EvanLandau/modular-housing-system/Wall Cores/basic_wall.FCStd

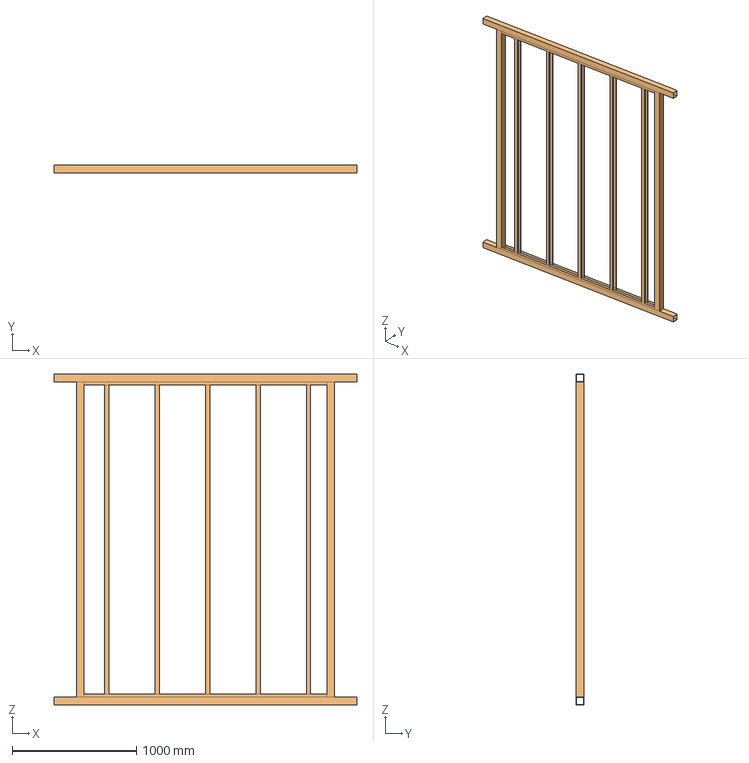
[picture p15: CAD file, 2021-06-02]
Wall Cores/basic_wall.FCStd
2438.4 x 63.5 x 2667.0 mm
Wall Inner Panel
Wall Inner Panel - Basic
