EvanLandau/modular-housing-system/Core Modules/medium_roof_slope_inside_corner.FCStd

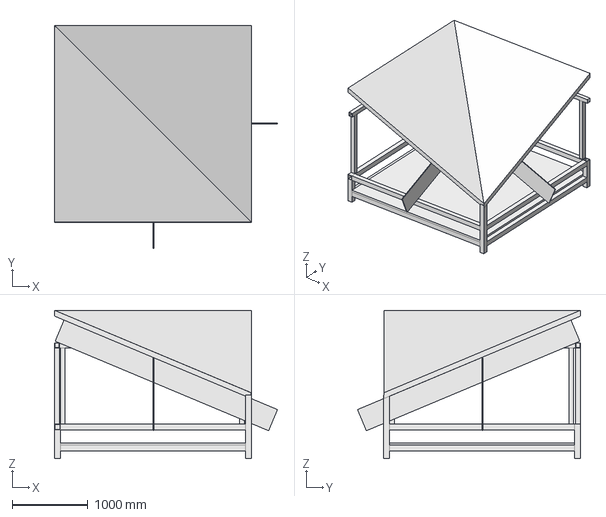
[picture p16: CAD file, 2021-06-02]
Core Modules/medium_roof_slope_inside_corner.FCStd
2936.2 x 2936.2 x 1953.9 mm
