EvanLandau/modular-housing-system/Core Modules/medium_roof_slope_outside_corner.FCStd

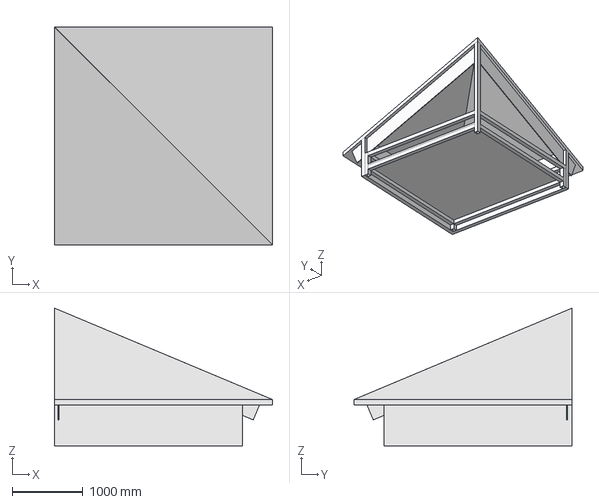
[picture p18: CAD file, 2021-06-02]
Core Modules/medium_roof_slope_outside_corner.FCStd
3092.4 x 3092.4 x 1953.8 mm
