EvanLandau/modular-housing-system/Other Modules/walk_in_closet.FCStd

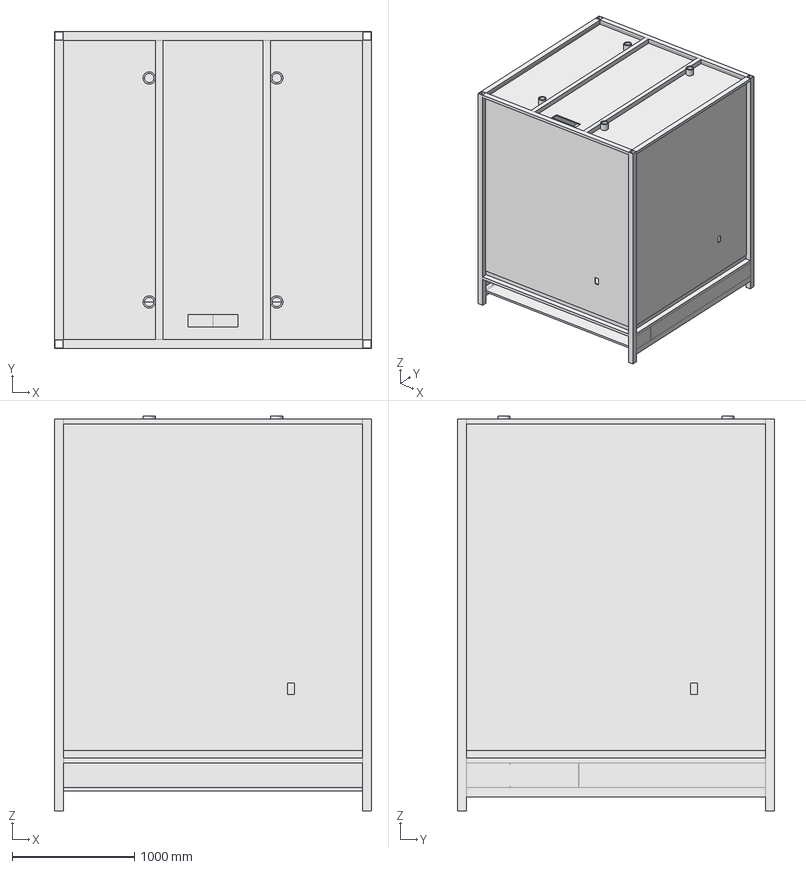
[picture p19: CAD file, 2021-06-02]
Other Modules/walk_in_closet.FCStd
2590.8 x 2590.8 x 3225.8 mm
