EvanLandau/modular-housing-system/Core Modules/bathroom_module.FCStd

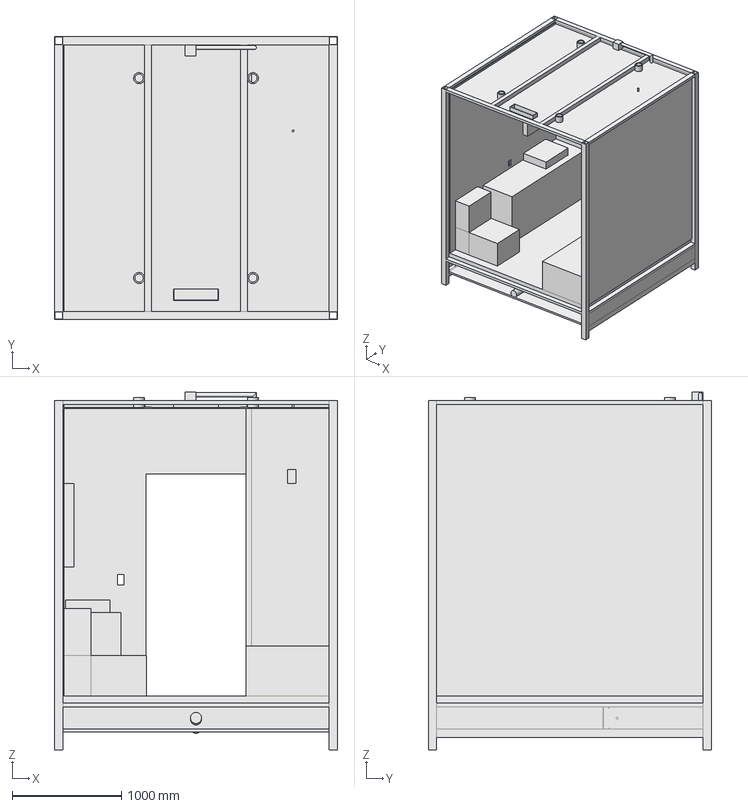
[picture p20: CAD file, 2021-06-02]
Core Modules/bathroom_module.FCStd
2590.8 x 2592.8 x 3276.6 mm
