EvanLandau/modular-housing-system/Other Modules/TV_room.FCStd

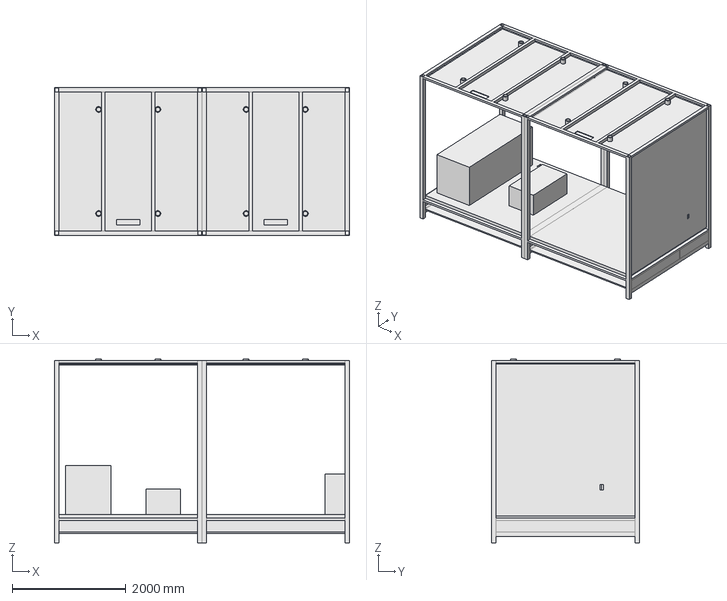
[picture p21: CAD file, 2021-06-02]
Other Modules/TV_room.FCStd
5181.6 x 2590.8 x 3225.8 mm
