EvanLandau/modular-housing-system/Core Modules/bedroom_module.FCStd

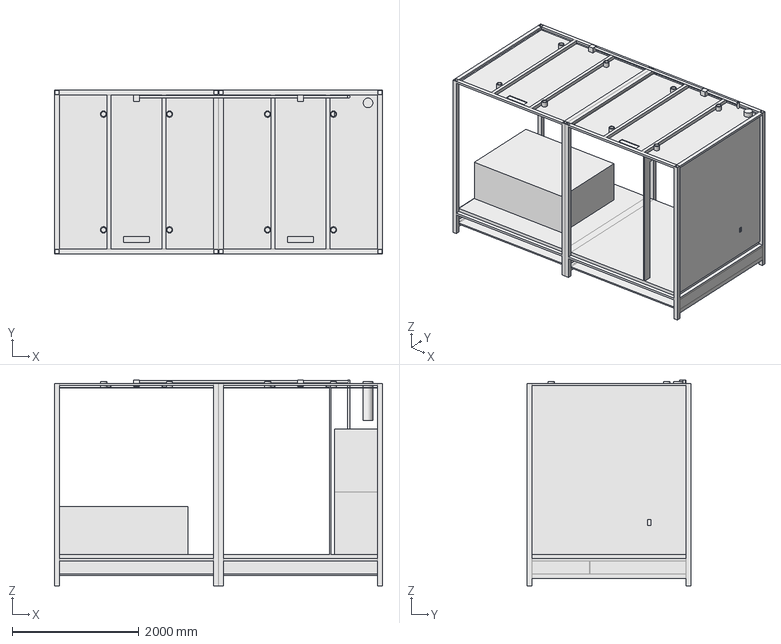
[picture p22: CAD file, 2021-06-02]
Core Modules/bedroom_module.FCStd
5181.6 x 2590.8 x 3251.2 mm
