EvanLandau/modular-housing-system/Other Modules/hall module.FCStd

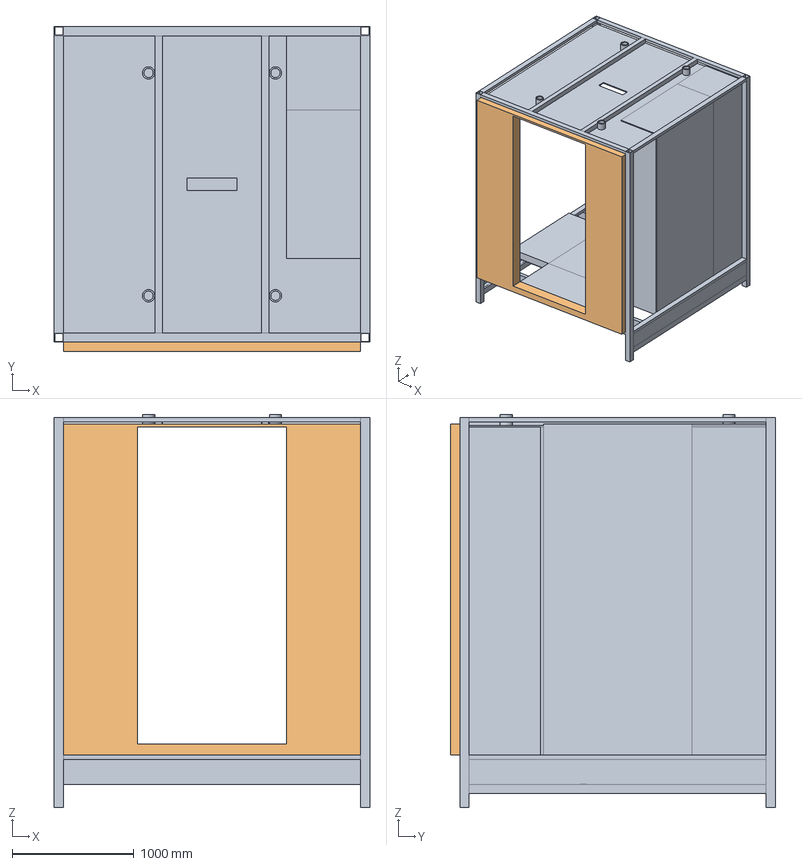
[picture p23: CAD file, 2021-06-02]
Other Modules/hall module.FCStd
2590.8 x 2667.0 x 3225.8 mm
Hall Module
Hall Connector
Hall Connector - Basic
