EvanLandau/modular-housing-system/Core Modules/stair_modules.FCStd

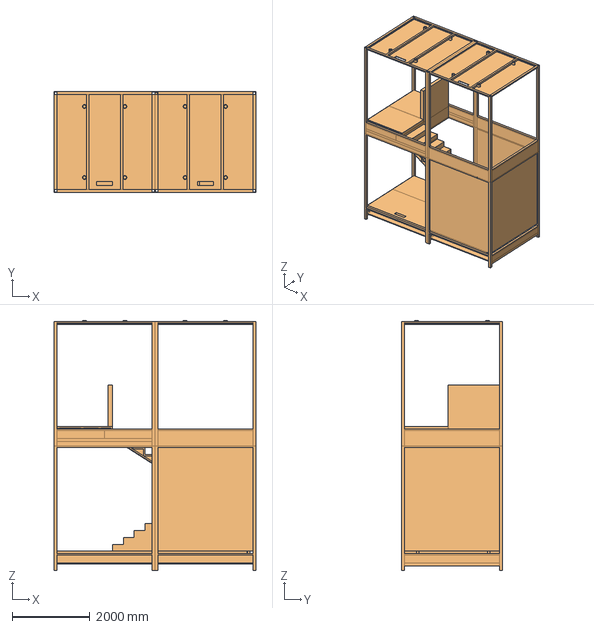
[picture p24: CAD file, 2021-06-02]
Core Modules/stair_modules.FCStd
5181.6 x 2590.8 x 6426.2 mm
Staircase
Staircase - Basic
