EvanLandau/modular-housing-system/Other Modules/office_module.FCStd

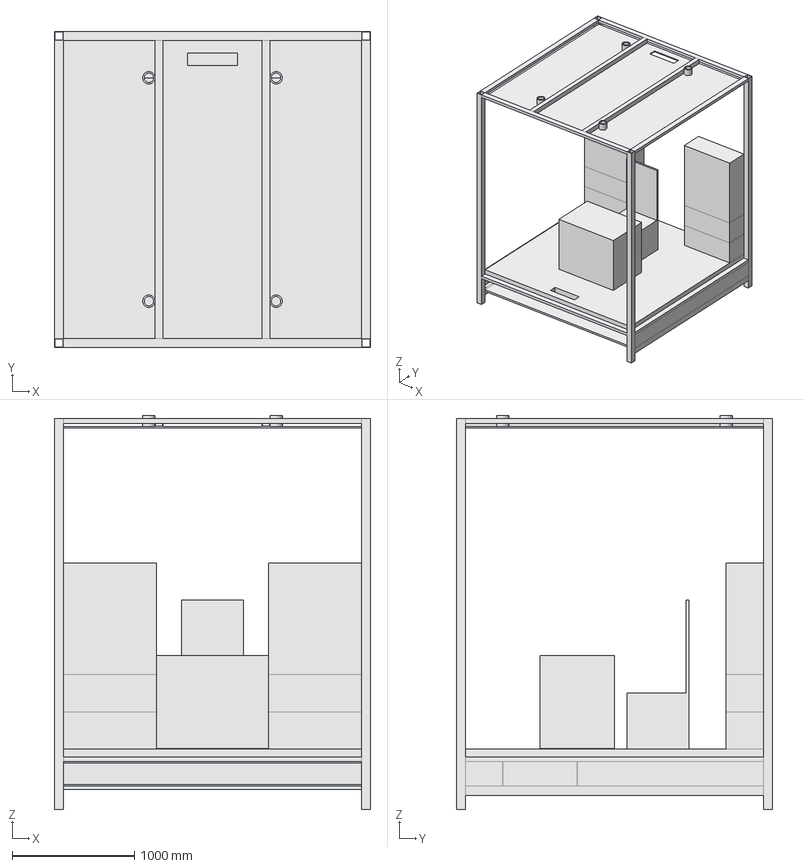
[picture p25: CAD file, 2021-06-02]
Other Modules/office_module.FCStd
2590.8 x 2590.8 x 3225.8 mm
